TDA-2030/vesc-remote-controller/mininrf/O1CN01XpR0Wq1Qkuaa4X6eF_!!2658592015.png

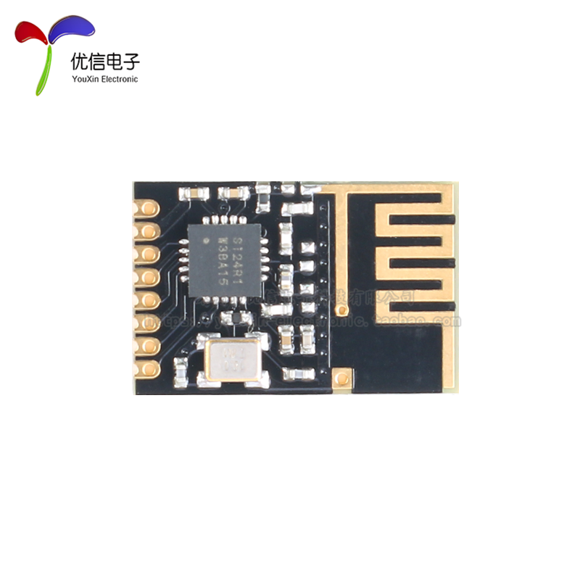
mininrf/O1CN01XpR0Wq1Qkuaa4X6eF_!!2658592015.png
