TDA-2030/vesc-remote-controller/mininrf/实物NRF.PNG

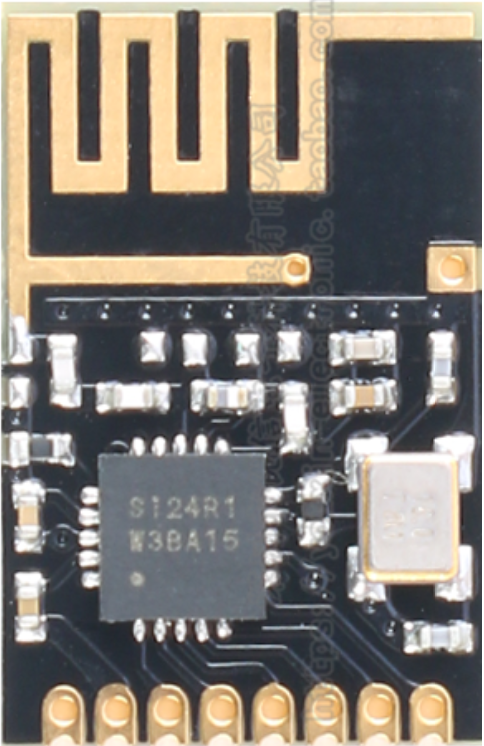
mininrf/实物NRF.PNG
