TDA-2030/vesc-remote-controller/mininrf/捕获.PNG

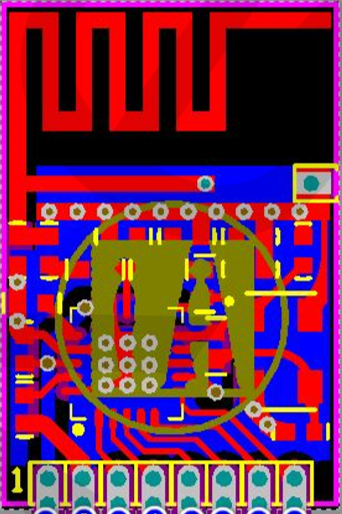
mininrf/捕获.PNG
