TDA-2030/vesc-remote-controller/PCB/TX-board-v2.0/STM8__TX.pdf

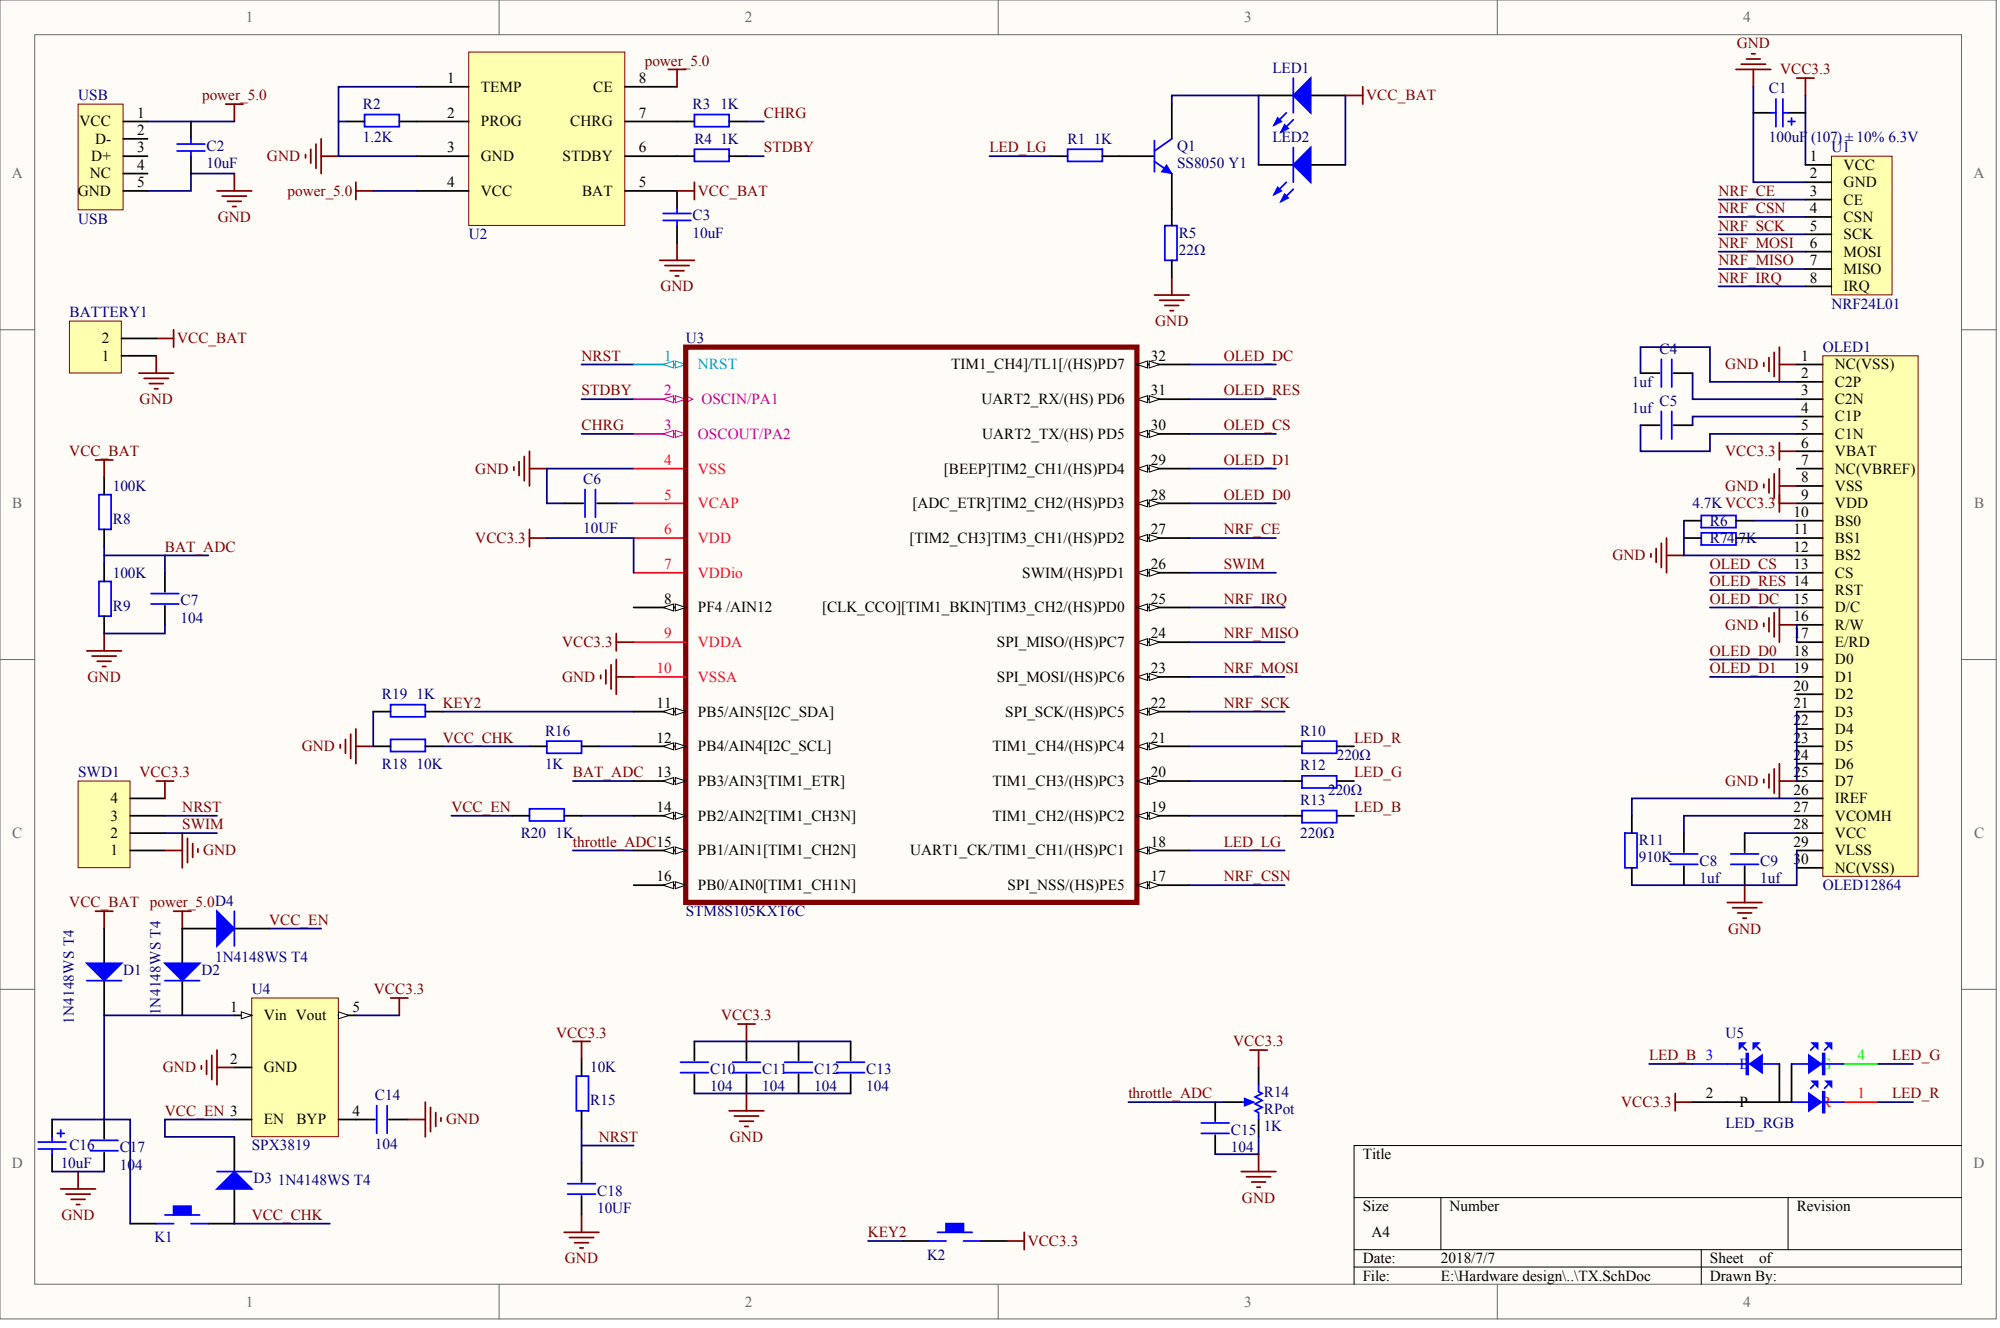
[picture p23: page 1]

VCOMH 27

VLSS 29

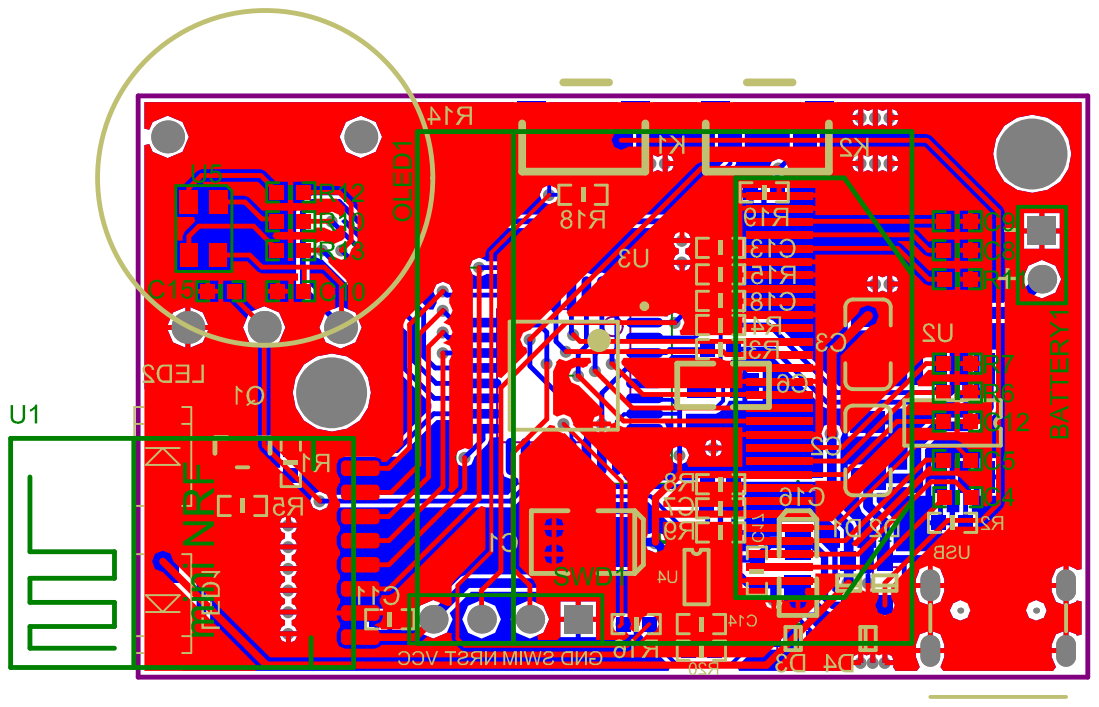
[picture p24: page 2]
