TDA-2030/vesc-remote-controller/PCB/RX-board-v1.0/STM8 remote.pdf

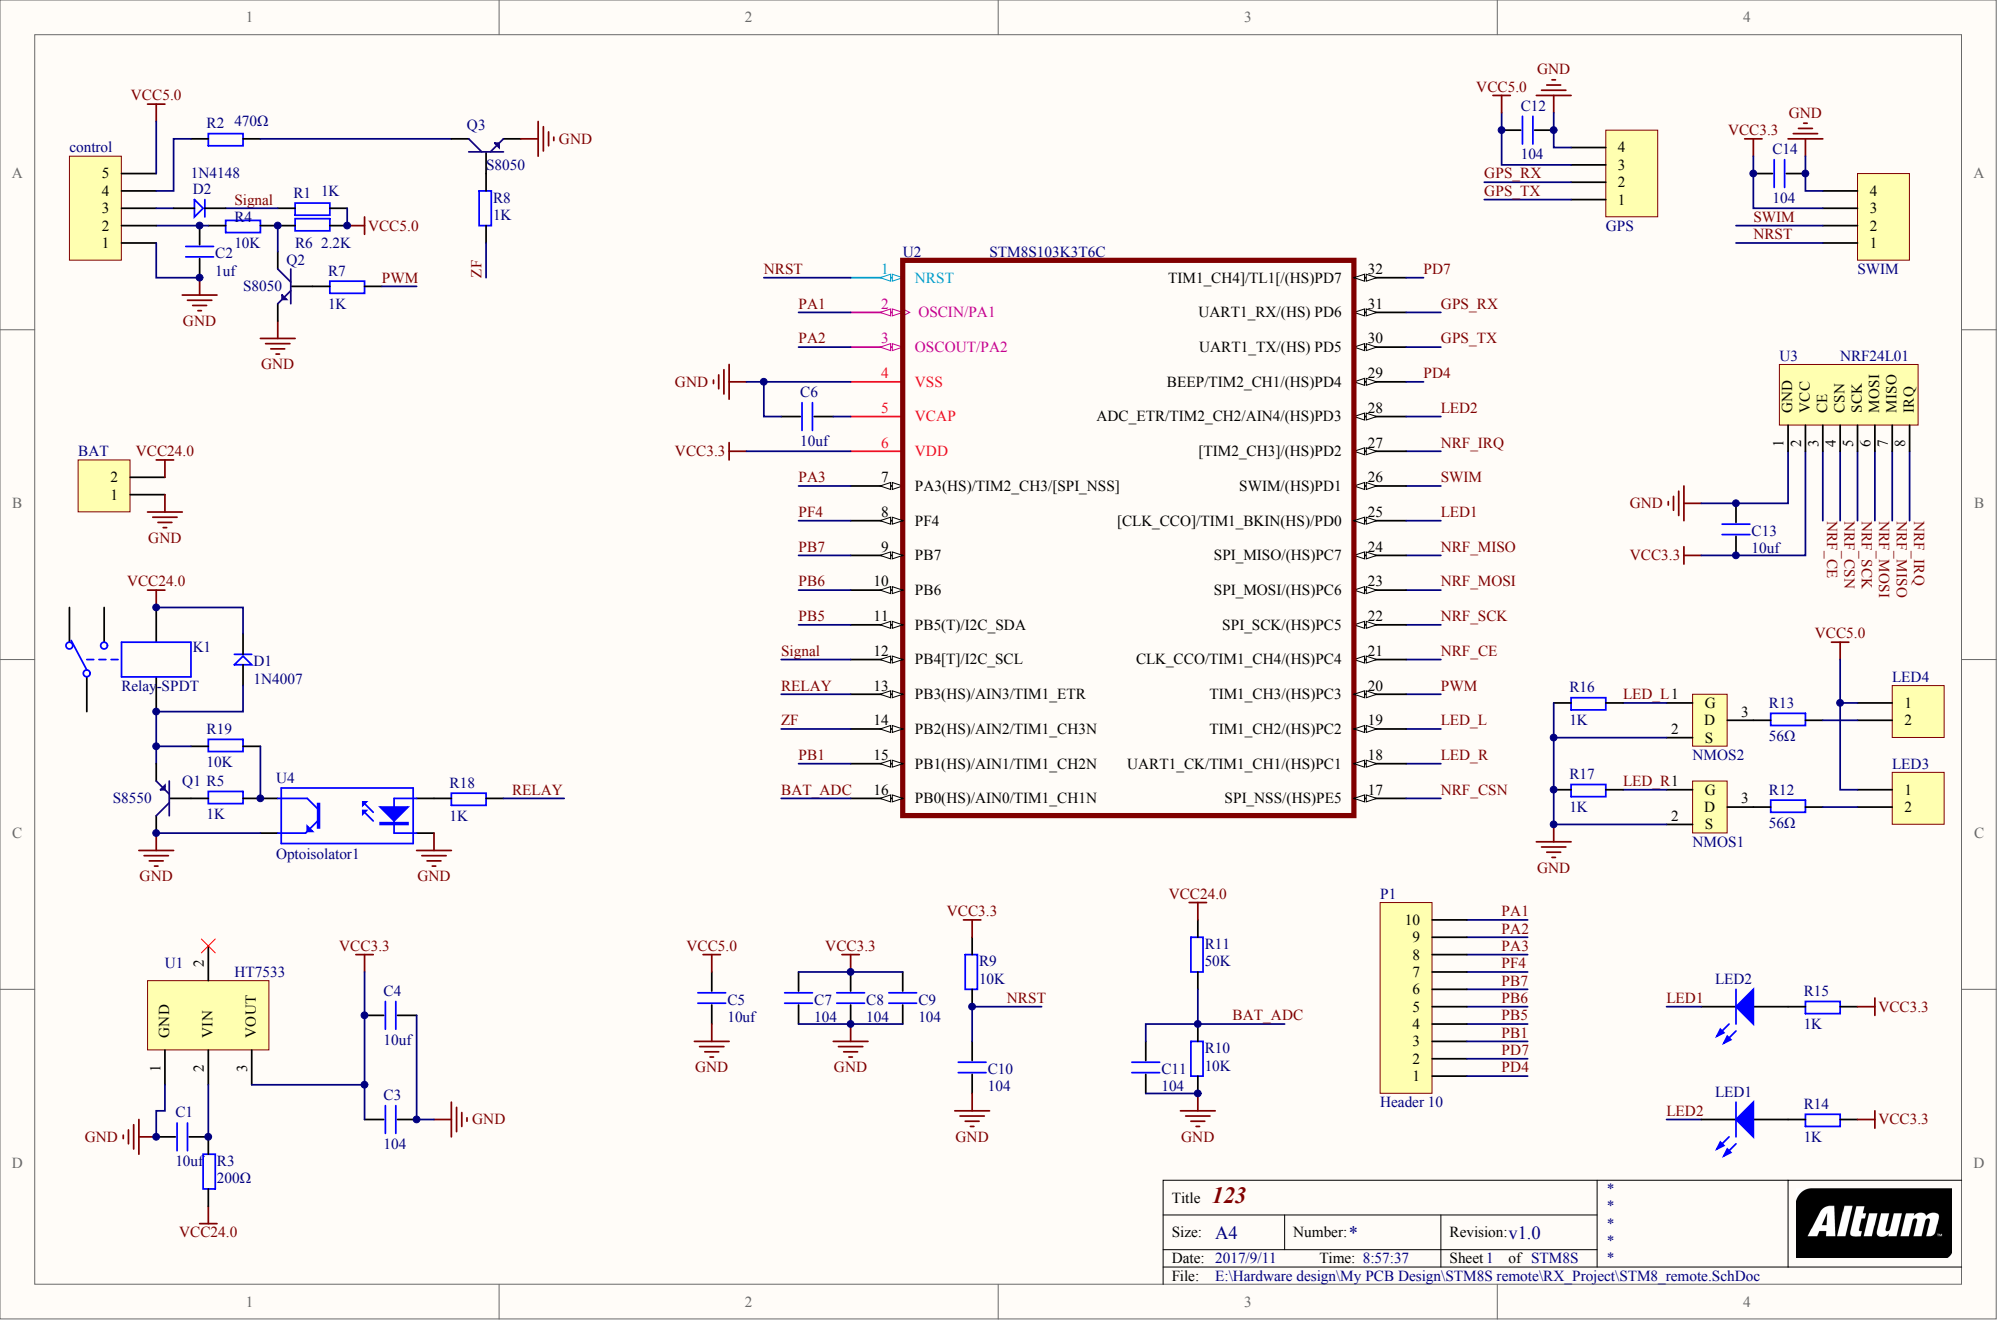
[picture p25: page 1]

123 Title | **** *

Size: A 4 | Number: * | Revision: v1.0

Date: File: 2017/9/11 Time: 8:57:37 | | Sheet 1 of STM8S

E:\Hardware design\My PCB Design\STM8S remote\RX_Project\STM8_remote.SchDoc

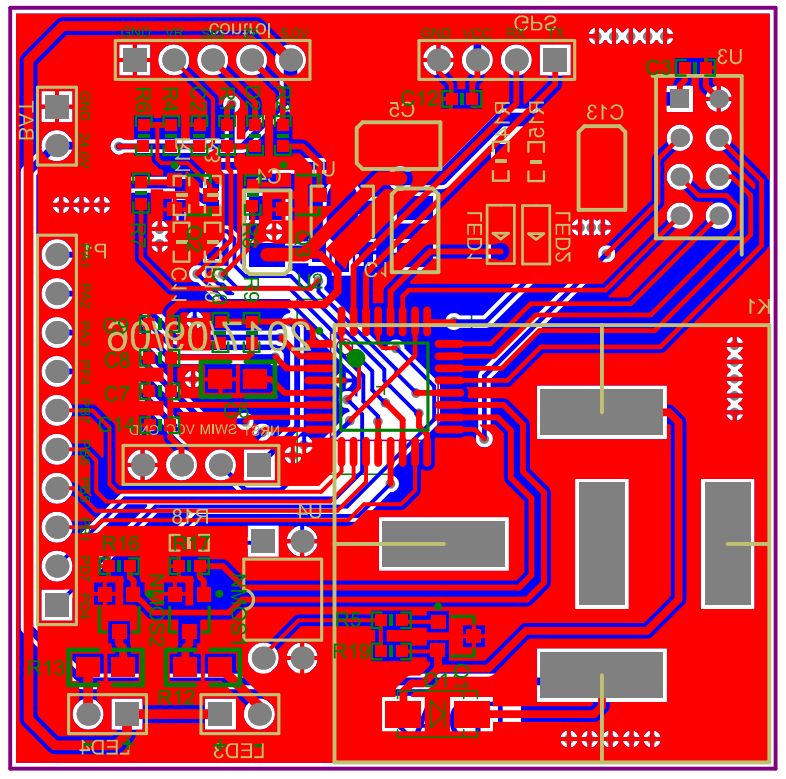
[picture p26: page 2]
