TDA-2030/vesc-remote-controller/PCB/RX-board-v2.0/RX.pdf

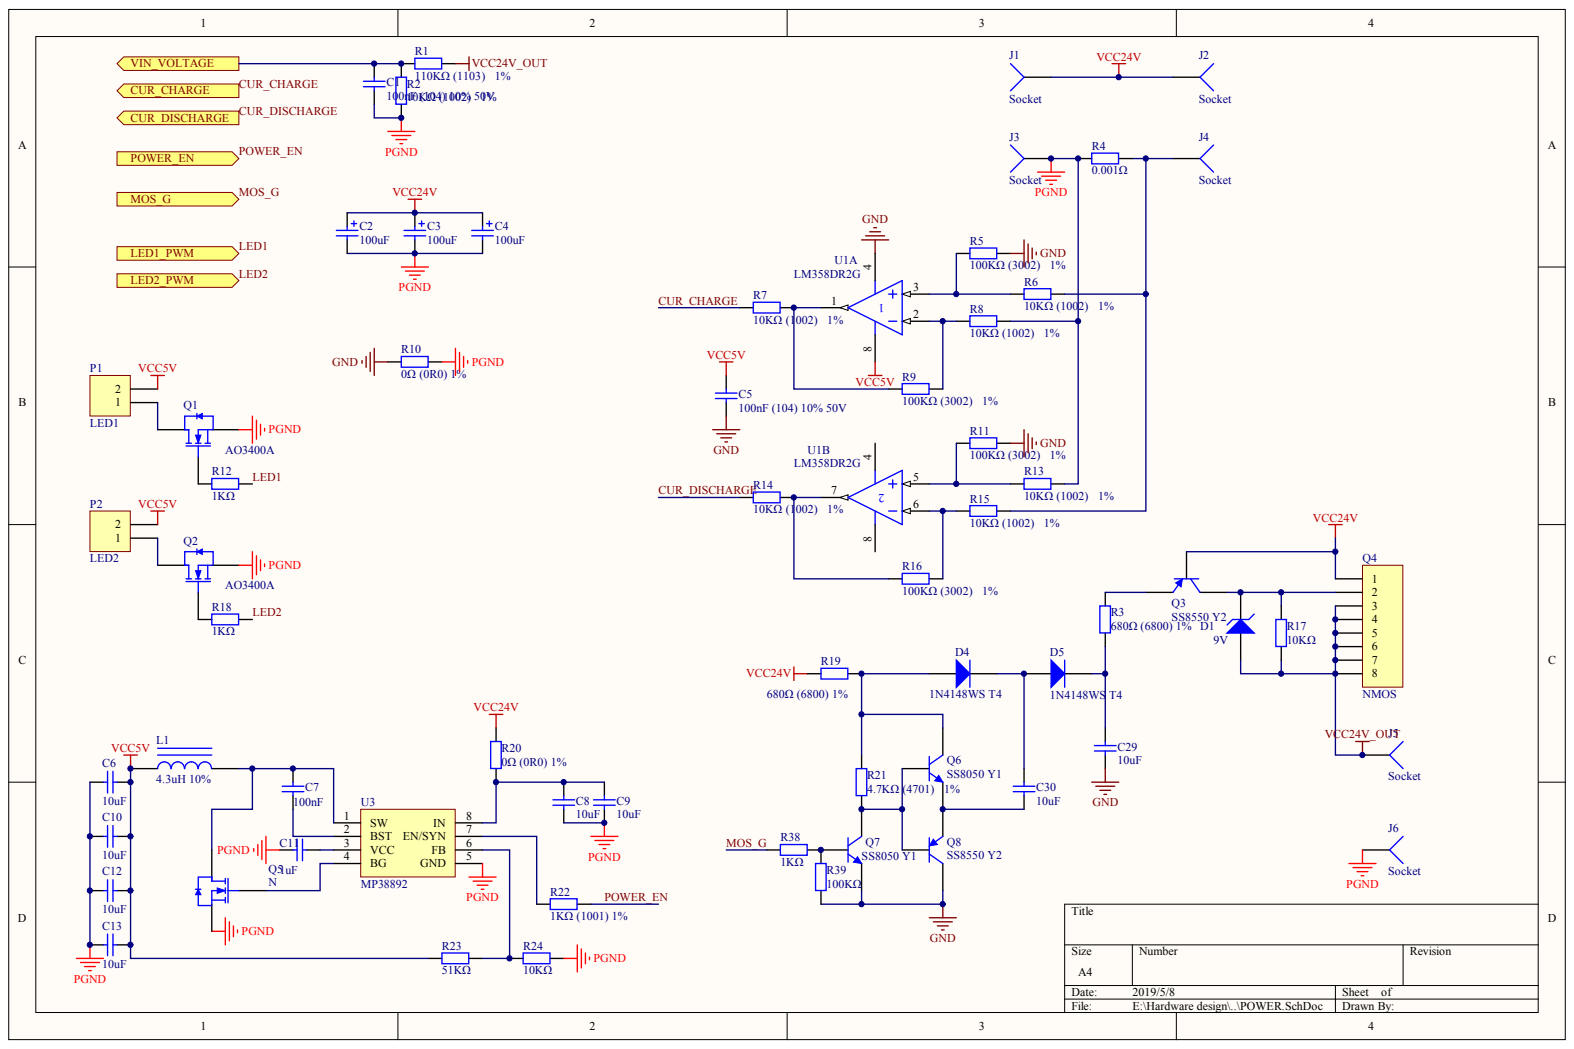
[picture p27: page 1]

Date: 2019/5/8 | Sheet of
File: E:\Hardware design\..\POWER.SchDoc | Drawn By:

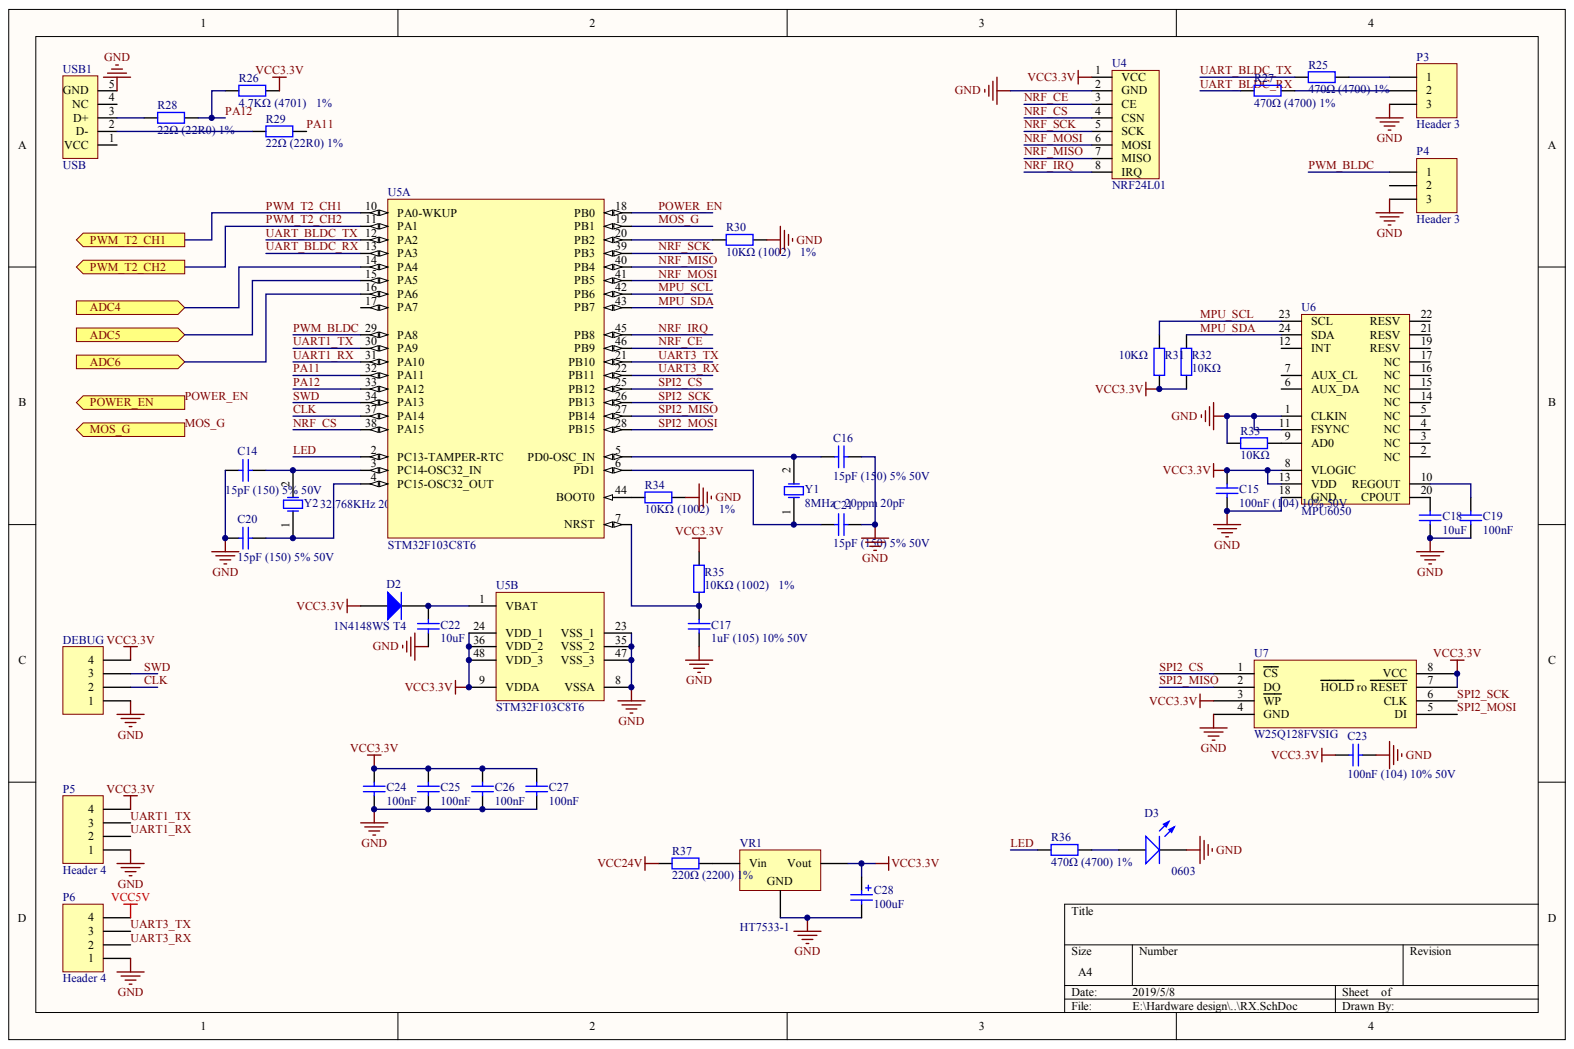
[picture p28: page 2]

PWM_BLDC | PA8 29

MPU_SDA | SDA 24

Size A4 | Number | Revision

Date: 2019/5/8 | Sheet of
File: E:\Hardware design\..\RX.SchDoc | Drawn By:

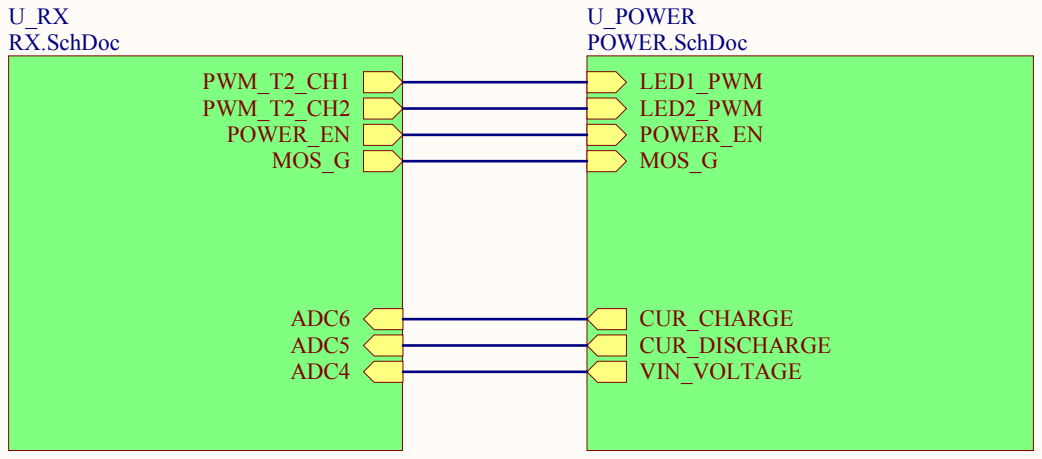
[picture p29: page 3]

Size A4 | Number | Revision

Date: 2019/5/8 | Sheet of
File: E:\Hardware design\..\TOP.SchDoc | Drawn By:

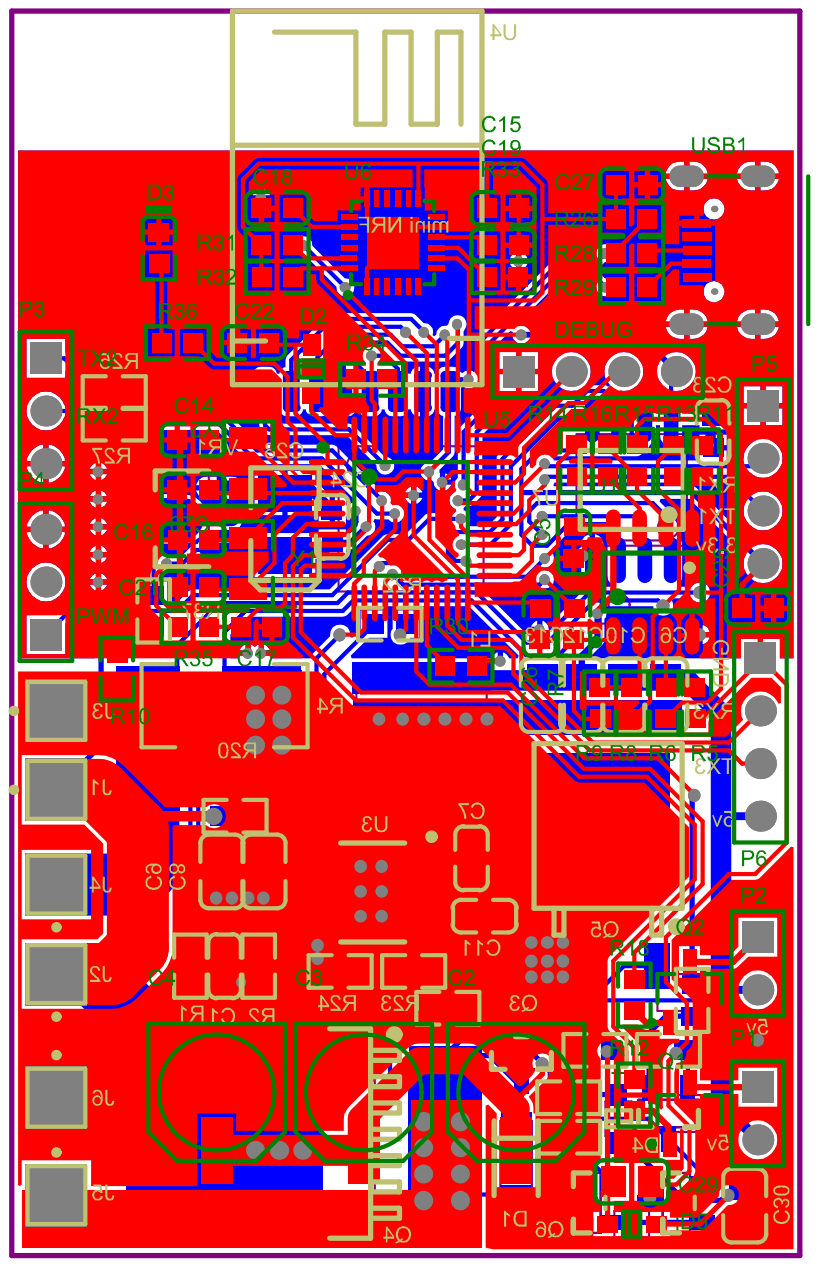
[picture p30: page 4]
