TDA-2030/vesc-remote-controller/PCB/RX-board-v4.0/RX.pdf

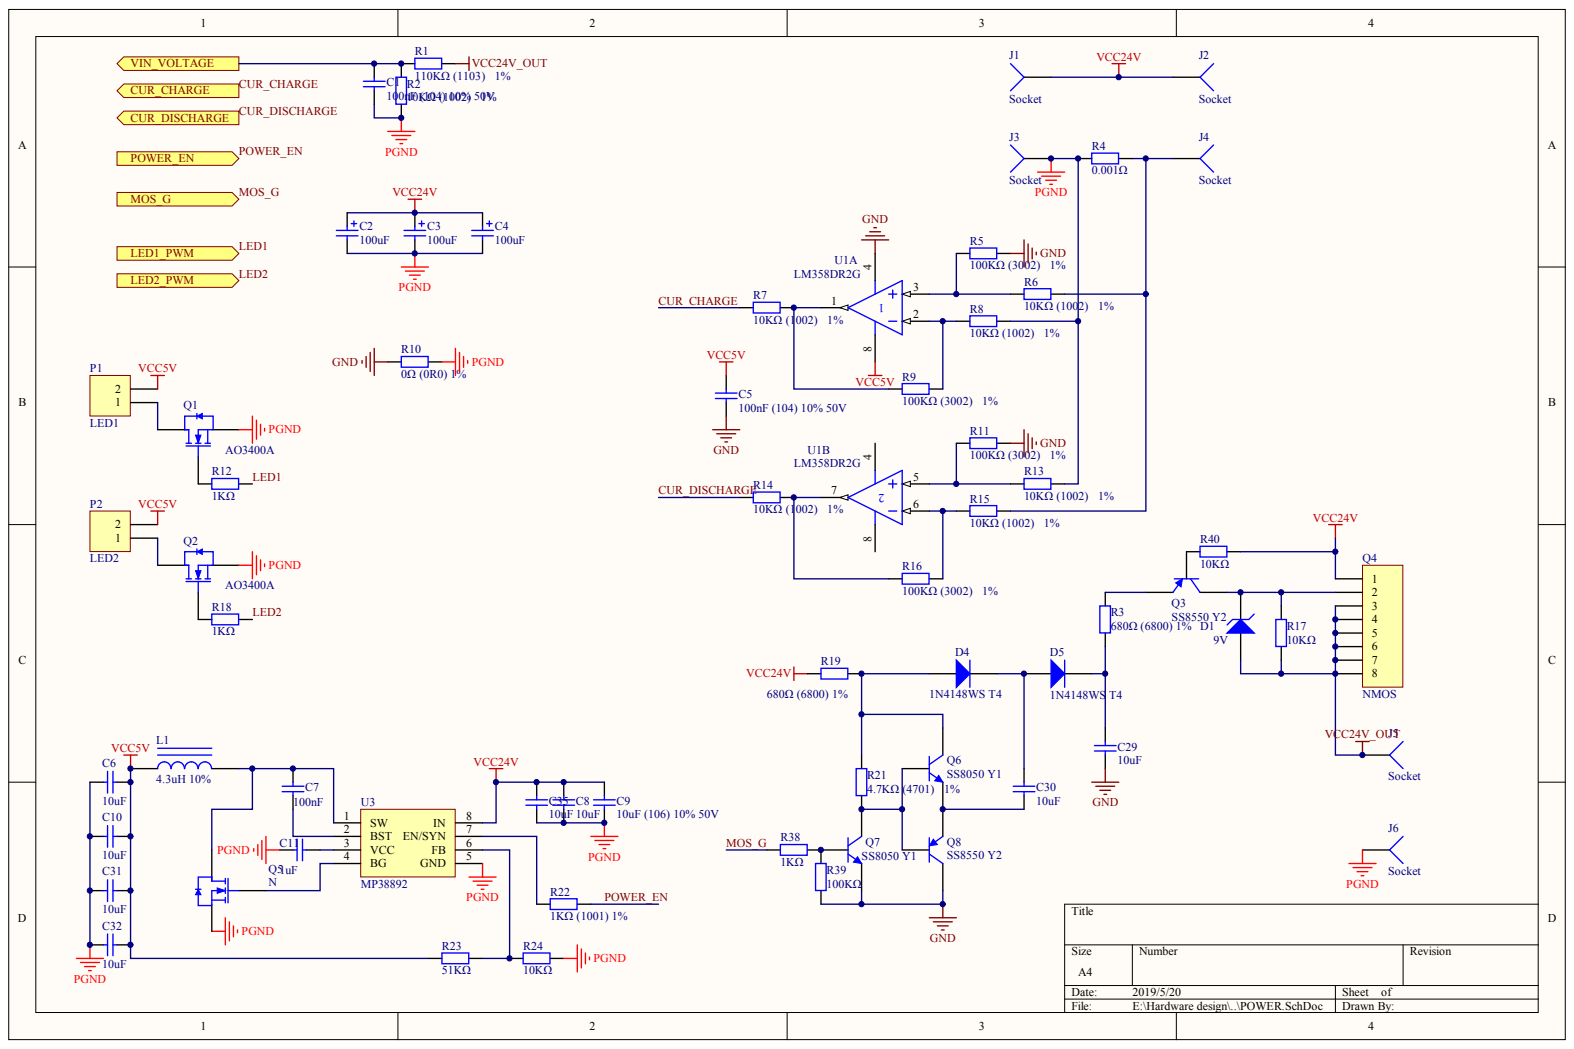
[picture p31: page 1]

Date: 2019/5/20 | Sheet of
File: E:\Hardware design\..\POWER.SchDoc | Drawn By:

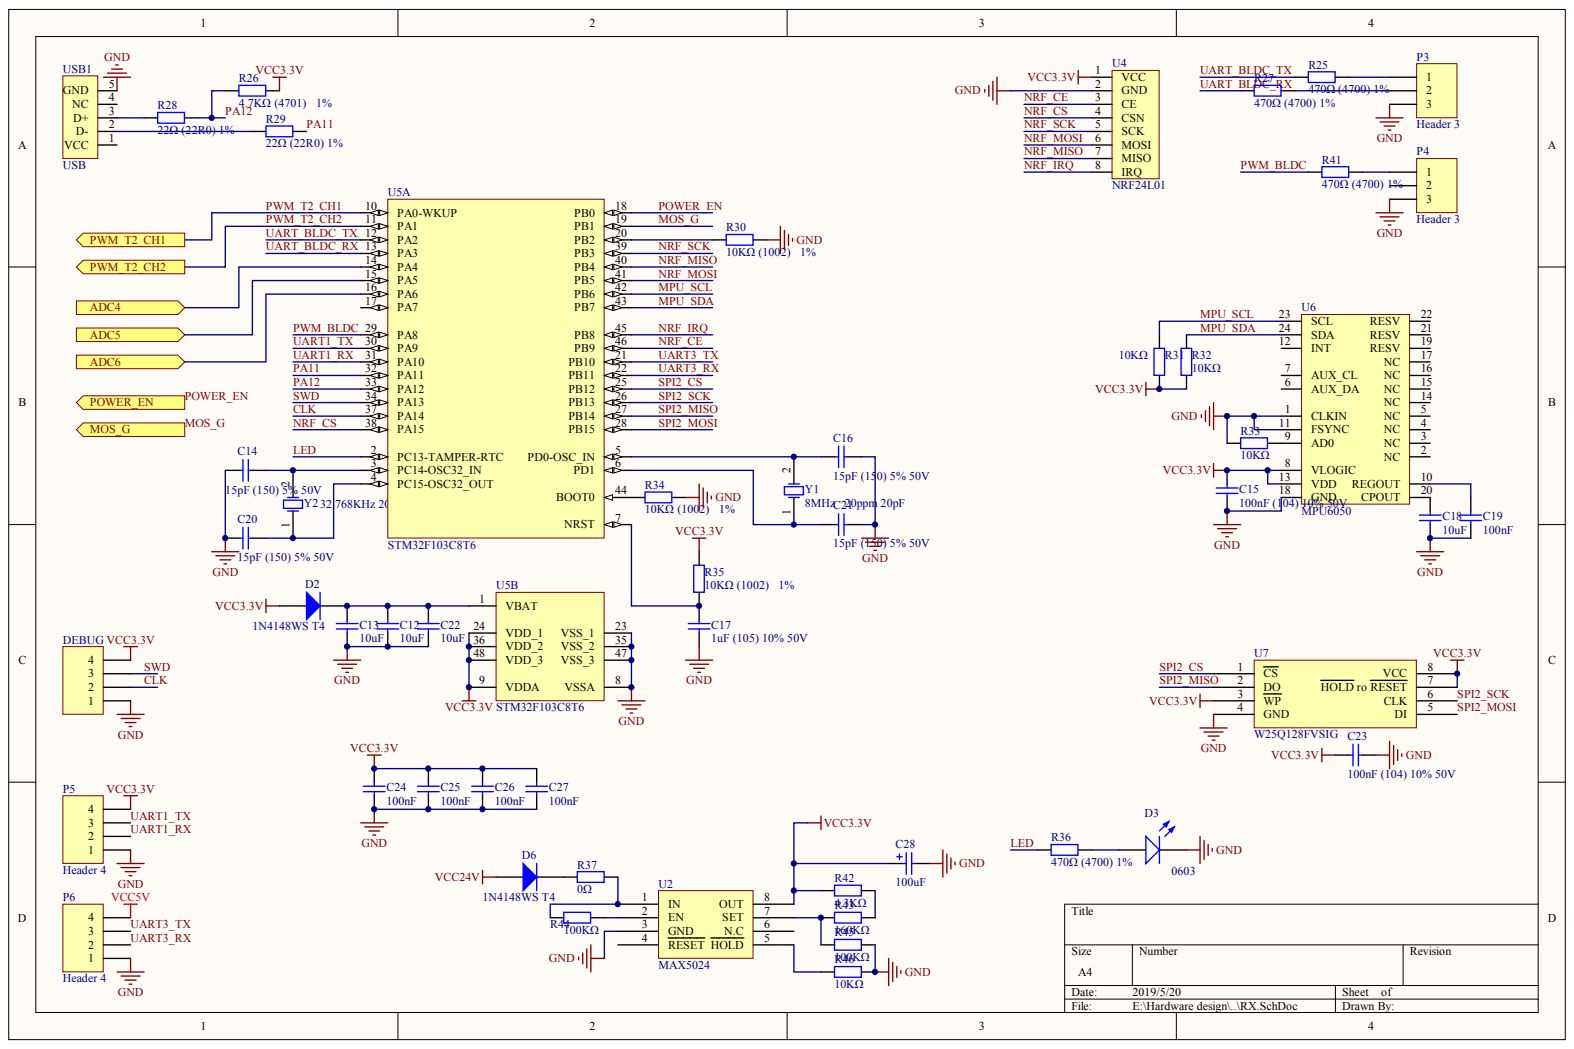
[picture p32: page 2]

PWM_BLDC | PA8 29

MPU_SDA | SDA 24

Size A4 | Number | Revision

Date: 2019/5/20 | Sheet of
File: E:\Hardware design\..\RX.SchDoc | Drawn By:


Size A4 | Number | Revision

Date: 2019/5/20 | Sheet of
File: E:\Hardware design\..\TOP.SchDoc | Drawn By:

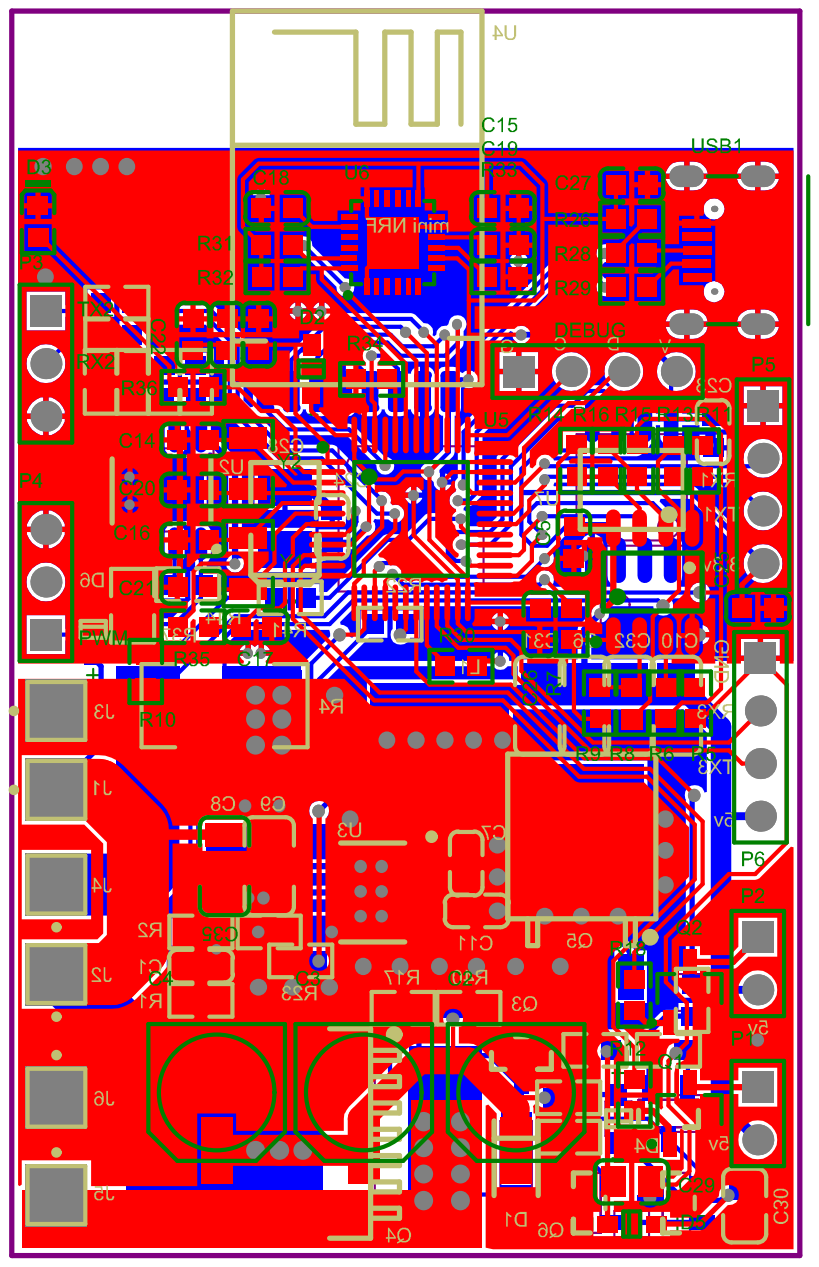
[picture p33: page 4]
