TDA-2030/vesc-remote-controller/receiver/code-L051K8U6/Src/tim.c

/**
  ******************************************************************************
  * File Name          : TIM.c
  * Description        : This file provides code for the configuration
  *                      of the TIM instances.
  ******************************************************************************
  * @attention
  *
  * <h2><center>&copy; Copyright (c) 2020 STMicroelectronics.
  * All rights reserved.</center></h2>
  *
  * This software component is licensed by ST under BSD 3-Clause license,
  * the "License"; You may not use this file except in compliance with the
  * License. You may obtain a copy of the License at:
  *                        opensource.org/licenses/BSD-3-Clause
  *
  ******************************************************************************
  */

/* Includes ------------------------------------------------------------------*/
#include "tim.h"

TIM_HandleTypeDef htim2;
TIM_HandleTypeDef htim6;
TIM_HandleTypeDef htim22;

/* TIM2 init function */
void MX_TIM2_Init(void)
{
  TIM_ClockConfigTypeDef sClockSourceConfig = {0};
  TIM_MasterConfigTypeDef sMasterConfig = {0};
  TIM_OC_InitTypeDef sConfigOC = {0};

  htim2.Instance = TIM2;
  htim2.Init.Prescaler = 31;
  htim2.Init.CounterMode = TIM_COUNTERMODE_UP;
  htim2.Init.Period = 19999;
  htim2.Init.ClockDivision = TIM_CLOCKDIVISION_DIV1;
  htim2.Init.AutoReloadPreload = TIM_AUTORELOAD_PRELOAD_ENABLE;
  if (HAL_TIM_Base_Init(&htim2) != HAL_OK)
  {
    Error_Handler();
  }
  sClockSourceConfig.ClockSource = TIM_CLOCKSOURCE_INTERNAL;
  if (HAL_TIM_ConfigClockSource(&htim2, &sClockSourceConfig) != HAL_OK)
  {
    Error_Handler();
  }
  if (HAL_TIM_PWM_Init(&htim2) != HAL_OK)
  {
    Error_Handler();
  }
  sMasterConfig.MasterOutputTrigger = TIM_TRGO_RESET;
  sMasterConfig.MasterSlaveMode = TIM_MASTERSLAVEMODE_DISABLE;
  if (HAL_TIMEx_MasterConfigSynchronization(&htim2, &sMasterConfig) != HAL_OK)
  {
    Error_Handler();
  }
  sConfigOC.OCMode = TIM_OCMODE_PWM1;
  sConfigOC.Pulse = 1500;
  sConfigOC.OCPolarity = TIM_OCPOLARITY_HIGH;
  sConfigOC.OCFastMode = TIM_OCFAST_DISABLE;
  if (HAL_TIM_PWM_ConfigChannel(&htim2, &sConfigOC, TIM_CHANNEL_1) != HAL_OK)
  {
    Error_Handler();
  }
  if (HAL_TIM_PWM_ConfigChannel(&htim2, &sConfigOC, TIM_CHANNEL_2) != HAL_OK)
  {
    Error_Handler();
  }
  if (HAL_TIM_PWM_ConfigChannel(&htim2, &sConfigOC, TIM_CHANNEL_4) != HAL_OK)
  {
    Error_Handler();
  }
  HAL_TIM_MspPostInit(&htim2);

}
/* TIM6 init function */
void MX_TIM6_Init(void)
{
  TIM_MasterConfigTypeDef sMasterConfig = {0};

  htim6.Instance = TIM6;
  htim6.Init.Prescaler = 31;
  htim6.Init.CounterMode = TIM_COUNTERMODE_UP;
  htim6.Init.Period = 4999;
  htim6.Init.AutoReloadPreload = TIM_AUTORELOAD_PRELOAD_ENABLE;
  if (HAL_TIM_Base_Init(&htim6) != HAL_OK)
  {
    Error_Handler();
  }
  sMasterConfig.MasterOutputTrigger = TIM_TRGO_RESET;
  sMasterConfig.MasterSlaveMode = TIM_MASTERSLAVEMODE_DISABLE;
  if (HAL_TIMEx_MasterConfigSynchronization(&htim6, &sMasterConfig) != HAL_OK)
  {
    Error_Handler();
  }

}
/* TIM22 init function */
void MX_TIM22_Init(void)
{
  TIM_ClockConfigTypeDef sClockSourceConfig = {0};
  TIM_MasterConfigTypeDef sMasterConfig = {0};
  TIM_OC_InitTypeDef sConfigOC = {0};

  htim22.Instance = TIM22;
  htim22.Init.Prescaler = 31;
  htim22.Init.CounterMode = TIM_COUNTERMODE_UP;
  htim22.Init.Period = 999;
  htim22.Init.ClockDivision = TIM_CLOCKDIVISION_DIV1;
  htim22.Init.AutoReloadPreload = TIM_AUTORELOAD_PRELOAD_ENABLE;
  if (HAL_TIM_Base_Init(&htim22) != HAL_OK)
  {
    Error_Handler();
  }
  sClockSourceConfig.ClockSource = TIM_CLOCKSOURCE_INTERNAL;
  if (HAL_TIM_ConfigClockSource(&htim22, &sClockSourceConfig) != HAL_OK)
  {
    Error_Handler();
  }
  if (HAL_TIM_OC_Init(&htim22) != HAL_OK)
  {
    Error_Handler();
  }
  sMasterConfig.MasterOutputTrigger = TIM_TRGO_RESET;
  sMasterConfig.MasterSlaveMode = TIM_MASTERSLAVEMODE_DISABLE;
  if (HAL_TIMEx_MasterConfigSynchronization(&htim22, &sMasterConfig) != HAL_OK)
  {
    Error_Handler();
  }
  sConfigOC.OCMode = TIM_OCMODE_TIMING;
  sConfigOC.Pulse = 500;
  sConfigOC.OCPolarity = TIM_OCPOLARITY_HIGH;
  sConfigOC.OCFastMode = TIM_OCFAST_DISABLE;
  if (HAL_TIM_OC_ConfigChannel(&htim22, &sConfigOC, TIM_CHANNEL_1) != HAL_OK)
  {
    Error_Handler();
  }
  HAL_TIM_MspPostInit(&htim22);

}

void HAL_TIM_Base_MspInit(TIM_HandleTypeDef* tim_baseHandle)
{

  if(tim_baseHandle->Instance==TIM2)
  {
    /* TIM2 clock enable */
    __HAL_RCC_TIM2_CLK_ENABLE();
  }
  else if(tim_baseHandle->Instance==TIM6)
  {
    /* TIM6 clock enable */
    __HAL_RCC_TIM6_CLK_ENABLE();

    /* TIM6 interrupt Init */
    HAL_NVIC_SetPriority(TIM6_DAC_IRQn, 0, 0);
    HAL_NVIC_EnableIRQ(TIM6_DAC_IRQn);
  }
  else if(tim_baseHandle->Instance==TIM22)
  {
    /* TIM22 clock enable */
    __HAL_RCC_TIM22_CLK_ENABLE();
  }
}
void HAL_TIM_MspPostInit(TIM_HandleTypeDef* timHandle)
{

  GPIO_InitTypeDef GPIO_InitStruct = {0};
  if(timHandle->Instance==TIM2)
  {
    __HAL_RCC_GPIOA_CLK_ENABLE();
    /**TIM2 GPIO Configuration    
    PA0     ------> TIM2_CH1
    PA1     ------> TIM2_CH2
    PA3     ------> TIM2_CH4 
    */
    GPIO_InitStruct.Pin = GPIO_PIN_0|GPIO_PIN_1|GPIO_PIN_3;
    GPIO_InitStruct.Mode = GPIO_MODE_AF_PP;
    GPIO_InitStruct.Pull = GPIO_NOPULL;
    GPIO_InitStruct.Speed = GPIO_SPEED_FREQ_LOW;
    GPIO_InitStruct.Alternate = GPIO_AF2_TIM2;
    HAL_GPIO_Init(GPIOA, &GPIO_InitStruct);

  }
  else if(timHandle->Instance==TIM22)
  {
  
    __HAL_RCC_GPIOB_CLK_ENABLE();
    /**TIM22 GPIO Configuration    
    PB4     ------> TIM22_CH1 
    */
    GPIO_InitStruct.Pin = GPIO_PIN_4;
    GPIO_InitStruct.Mode = GPIO_MODE_AF_PP;
    GPIO_InitStruct.Pull = GPIO_NOPULL;
    GPIO_InitStruct.Speed = GPIO_SPEED_FREQ_LOW;
    GPIO_InitStruct.Alternate = GPIO_AF4_TIM22;
    HAL_GPIO_Init(GPIOB, &GPIO_InitStruct);

  }

}

void HAL_TIM_Base_MspDeInit(TIM_HandleTypeDef* tim_baseHandle)
{

  if(tim_baseHandle->Instance==TIM2)
  {
    /* Peripheral clock disable */
    __HAL_RCC_TIM2_CLK_DISABLE();
  }
  else if(tim_baseHandle->Instance==TIM6)
  {
    /* Peripheral clock disable */
    __HAL_RCC_TIM6_CLK_DISABLE();

    /* TIM6 interrupt Deinit */
    HAL_NVIC_DisableIRQ(TIM6_DAC_IRQn);
  }
  else if(tim_baseHandle->Instance==TIM22)
  {
    /* Peripheral clock disable */
    __HAL_RCC_TIM22_CLK_DISABLE();
  }
} 

/* USER CODE BEGIN 1 */

void throttle_init(void)
{
	MX_TIM2_Init();
	HAL_TIM_PWM_Start(&htim2, TIM_CHANNEL_1);
	__HAL_TIM_SetCompare(&htim2, TIM_CHANNEL_1, 0);
}

void throttle_set(uint16_t throttle)
{
	
	if(throttle>THROTTLE_MAX)
	{
		throttle = THROTTLE_MAX;
	}
	__HAL_TIM_SetCompare(&htim2, TIM_CHANNEL_1, 999+throttle);
}



void bootstrap_init(void)
{
	MX_TIM22_Init();
	HAL_TIM_PWM_Start(&htim22, TIM_CHANNEL_1);
	__HAL_TIM_SetCompare(&htim22, TIM_CHANNEL_1, 0);
}

void bootstrap_enable(uint8_t state)
{
	GPIO_InitTypeDef GPIO_InitStruct = {0};
	if(state)
	{
		
		GPIO_InitStruct.Pin = GPIO_PIN_4;
		GPIO_InitStruct.Mode = GPIO_MODE_AF_PP;
		GPIO_InitStruct.Pull = GPIO_NOPULL;
		GPIO_InitStruct.Speed = GPIO_SPEED_FREQ_LOW;
		GPIO_InitStruct.Alternate = GPIO_AF4_TIM22;
		HAL_GPIO_Init(GPIOB, &GPIO_InitStruct);
		
		HAL_TIM_PWM_Start(&htim22, TIM_CHANNEL_1);
	}
	else
	{
		
		HAL_TIM_PWM_Stop(&htim22, TIM_CHANNEL_1);
		
		GPIO_InitStruct.Pin = GPIO_PIN_4;
		GPIO_InitStruct.Mode = GPIO_MODE_INPUT;
		GPIO_InitStruct.Pull = GPIO_PULLDOWN;		
		GPIO_InitStruct.Speed = GPIO_SPEED_FREQ_LOW;
		HAL_GPIO_Init(GPIOB, &GPIO_InitStruct);
	}
}

uint8_t bootstrap_isenable(void)
{
	return ((&htim22)->Instance->CR1 & TIM_CR1_CEN)?1:0;
}


void light_init(void)
{
	//MX_TIM2_Init();  //油门那里已经初始化了
	HAL_TIM_PWM_Start(&htim2, TIM_CHANNEL_2);
	HAL_TIM_PWM_Start(&htim2, TIM_CHANNEL_4);
	__HAL_TIM_SetCompare(&htim2, TIM_CHANNEL_2, 0);
	__HAL_TIM_SetCompare(&htim2, TIM_CHANNEL_4, 0);
}

void light_set(uint8_t ch ,uint32_t val)
{
	if(val>100)val=100;
	if(1 == ch)
	{
		__HAL_TIM_SetCompare(&htim2, TIM_CHANNEL_2, val*1000/100);
	}
	else if(2 == ch)
	{
		__HAL_TIM_SetCompare(&htim2, TIM_CHANNEL_4, val*1000/100);
	}
}
/* USER CODE END 1 */

/************************ (C) COPYRIGHT STMicroelectronics *****END OF FILE****/
