TDA-2030/vesc-remote-controller/transmitter/code-STM8S/Source/inc/main.h

/*
 * @Author: zhouli
 * @Date: 2020-04-04 15:28:44
 * @LastEditTime: 2020-06-03 00:06:13
 * @Description: file content
 */ 


#ifndef _MAIN_H__
#define _MAIN_H__

#define SETTING_FLASH_ADDR (0)
#define FLASH_CHECK (0x1278)   //检验值

#define MAJOR_VERSION 2
#define MINOR_VERSION 1


typedef struct
{
    uint16_t check;

    uint32_t *dashboard_p1;
    uint32_t *dashboard_p2;
    uint8_t light_en;
    uint8_t light1;
    uint8_t light2;

    uint16_t auto_off_time;

} Setting_TypeDef;
extern Setting_TypeDef setting;


typedef struct
{
    volatile uint8_t state;
    uint16_t auto_off_timer;
	uint16_t bat_vol;

} System_TypeDef;
extern System_TypeDef system;

typedef enum
{
    SYSTEM_STATE_IDLE,     //已连接，未开机
    SYSTEM_STATE_RUNNING,  //运行中
    SYSTEM_STATE_CHARGING, //充电中
    SYSTEM_STATE_NO_SIGNAL,//信号丢失
};

extern uint32_t Sys_Time;

void setting_write(void);
void setting_read(void);

#endif
