TDA-2030/vesc-remote-controller/receiver/code-L051K8U6/Src/rtc.c

/**
  ******************************************************************************
  * File Name          : RTC.c
  * Description        : This file provides code for the configuration
  *                      of the RTC instances.
  ******************************************************************************
  * @attention
  *
  * <h2><center>&copy; Copyright (c) 2020 STMicroelectronics.
  * All rights reserved.</center></h2>
  *
  * This software component is licensed by ST under BSD 3-Clause license,
  * the "License"; You may not use this file except in compliance with the
  * License. You may obtain a copy of the License at:
  *                        opensource.org/licenses/BSD-3-Clause
  *
  ******************************************************************************
  */

/* Includes ------------------------------------------------------------------*/
#include "rtc.h"

/* USER CODE BEGIN 0 */


_calendar_obj calendar;//ʱ�ӽṹ�� 


/* USER CODE END 0 */

RTC_HandleTypeDef hrtc;

/* RTC init function */
void MX_RTC_Init(void)
{
  RTC_TimeTypeDef sTime = {0};
  RTC_DateTypeDef sDate = {0};

  /** Initialize RTC Only 
  */
  hrtc.Instance = RTC;
  hrtc.Init.HourFormat = RTC_HOURFORMAT_24;
  hrtc.Init.AsynchPrediv = 127;
  hrtc.Init.SynchPrediv = 255;
  hrtc.Init.OutPut = RTC_OUTPUT_DISABLE;
  hrtc.Init.OutPutRemap = RTC_OUTPUT_REMAP_NONE;
  hrtc.Init.OutPutPolarity = RTC_OUTPUT_POLARITY_HIGH;
  hrtc.Init.OutPutType = RTC_OUTPUT_TYPE_OPENDRAIN;
  if (HAL_RTC_Init(&hrtc) != HAL_OK)
  {
    Error_Handler();
  }

  /** Initialize RTC and set the Time and Date 
  */
  sTime.Hours = 0;
  sTime.Minutes = 0;
  sTime.Seconds = 0;
  sTime.DayLightSaving = RTC_DAYLIGHTSAVING_NONE;
  sTime.StoreOperation = RTC_STOREOPERATION_RESET;
  if (HAL_RTC_SetTime(&hrtc, &sTime, RTC_FORMAT_BIN) != HAL_OK)
  {
    Error_Handler();
  }
  sDate.WeekDay = RTC_WEEKDAY_SUNDAY;
  sDate.Month = RTC_MONTH_MARCH;
  sDate.Date = 1;
  sDate.Year = 20;

  if (HAL_RTC_SetDate(&hrtc, &sDate, RTC_FORMAT_BIN) != HAL_OK)
  {
    Error_Handler();
  }
  /** Enable the WakeUp 
  */

}

void HAL_RTC_MspInit(RTC_HandleTypeDef* rtcHandle)
{

  if(rtcHandle->Instance==RTC)
  {
    /* RTC clock enable */
    __HAL_RCC_RTC_ENABLE();

    /* RTC interrupt Init */
    HAL_NVIC_SetPriority(RTC_IRQn, 0, 0);
    HAL_NVIC_EnableIRQ(RTC_IRQn);
  }
}

void HAL_RTC_MspDeInit(RTC_HandleTypeDef* rtcHandle)
{

  if(rtcHandle->Instance==RTC)
  {
    /* Peripheral clock disable */
    __HAL_RCC_RTC_DISABLE();

    /* RTC interrupt Deinit */
    HAL_NVIC_DisableIRQ(RTC_IRQn);
  }
} 

/* USER CODE BEGIN 1 */

void RTC_Get(void)
{
	RTC_DateTypeDef rtc_data;
	RTC_TimeTypeDef rtc_time;
	
	HAL_RTC_GetTime(&hrtc, &rtc_time, RTC_FORMAT_BIN);
	HAL_RTC_GetDate(&hrtc, &rtc_data, RTC_FORMAT_BIN);
	
	
	calendar.w_year = rtc_data.Year;
	calendar.w_month = rtc_data.Month;
	calendar.w_date = rtc_data.Date;
	
	calendar.hour = rtc_time.Hours;
	calendar.min = rtc_time.Minutes;
	calendar.sec = rtc_time.Seconds;
}

uint8_t RTC_Set(uint16_t syear,uint8_t smon,uint8_t sday,uint8_t hour,uint8_t min,uint8_t sec)
{
	RTC_DateTypeDef rtc_data;
	RTC_TimeTypeDef rtc_time;
	
	rtc_time.DayLightSaving = RTC_DAYLIGHTSAVING_NONE;
	rtc_time.StoreOperation = RTC_STOREOPERATION_RESET;
	
	rtc_data.Year = syear;
	rtc_data.Month = smon;
	rtc_data.Date = sday;
	
	rtc_time.Hours = hour;
	rtc_time.Minutes = min;
	rtc_time.Seconds = sec;
	
	HAL_RTC_SetTime(&hrtc, &rtc_time, RTC_FORMAT_BIN);
	HAL_RTC_SetDate(&hrtc, &rtc_data, RTC_FORMAT_BIN);
	return 0;
}

/* USER CODE END 1 */

/************************ (C) COPYRIGHT STMicroelectronics *****END OF FILE****/
