TDA-2030/vesc-remote-controller/mininrf/2.NRF24L01程序/NRF24L01程序/双按键测试程序/inc/delay.h

/****************************************Copyright (c)**************************************************
**                               Guangzhou ZHIYUAN electronics Co.,LTD.
**                                     
**                                 http://www.embedtools.com
**
**--------------File Info-------------------------------------------------------------------------------
** File Name:         
** Last modified Date: 
** Last Version:       v1.00
** Description:        
** 
**------------------------------------------------------------------------------------------------------
** Created By:         
** Created date:       
** Version:            v1.00
** Descriptions:
**
**------------------------------------------------------------------------------------------------------
** Modified by:        
** Modified date:       
** Version:             
** Description:        
**
********************************************************************************************************/
#ifndef __DELAY_H
#define __DELAY_H
#include "typedef.h"

void _delay_us(unsigned int _us);
void Delay100ms(void);

#endif
