TDA-2030/vesc-remote-controller/mininrf/2.NRF24L01程序/NRF24L01程序/双按键测试程序/source/delay.c

/******************************************************************************/
/*                        -- 深圳安信可科技有限公司 --                        */
/*
//  文件名：                                                              
//  说明：                                                                  
//  编写人员：                                                                   
//  编写日期：                                                              
//  程序维护：
//  维护记录：
//
//                                                          
*/ 
// 免责声明：该程序仅用于学习与交流 
// (c) Anxinke Corporation. All rights reserved.                                                               
/******************************************************************************/
#include "delay.h"



/******************************************************************************/
// 函数名称： 
// 输入参数： 
// 输出参数： 
// 函数功能： 
/******************************************************************************/
void Delay100ms(void)       //@22.1184MHz
{
	unsigned char i, j, k;
	_nop_();
	_nop_();
	i = 9;
	j = 104;
	k = 139;
	do
	{
		do
		{
			while (--k);
		} while (--j);
	} while (--i);
}

/******************************************************************************/
// 函数名称： 
// 输入参数： 
// 输出参数： 
// 函数功能： 
/******************************************************************************/
void _delay_us(unsigned int _us)
{
    char a=0;
    for(_us;_us;_us--)
        for(a=0;a<1;a++);
}
