TDA-2030/vesc-remote-controller/transmitter/code-STM8S/Source/inc/m_settings.h

/*
 * @Author: zhouli
 * @Date: 2020-04-18 16:14:46
 * @LastEditTime: 2020-04-18 16:17:23
 * @Description: file content
 */

#ifndef __M_SETTINGS_H
#define __M_SETTINGS_H


void page_setting(void);

#endif
