TDA-2030/vesc-remote-controller/transmitter/code-STM8S/Source/inc/stm8s_flash.h

  
  
#ifndef __STM8S_FLASH_H__
#define __STM8S_FLASH_H__


void EEPROM_write(uint8_t addr,const uint8_t *indata,uint8_t inlength);
void EEPROM_read(uint8_t addr,uint8_t *indata,uint8_t inlength);


#endif
