TDA-2030/vesc-remote-controller/receiver/code-L051K8U6/Src/stmflash.c

#include "main.h"
#include "stmflash.h"

 


//读取指定地址的字(32位数据) 
//faddr:读地址 
//返回值:对应数据.
static uint32_t STMFLASH_ReadWord(uint32_t faddr)
{
	return *(__IO uint32_t *)faddr; 
}


//从指定地址开始写入指定长度的数据
//OTP区域地址范围:0X1FF0F000~0X1FF0F41F
//WriteAddr:起始地址(此地址必须为4的倍数!!)
//pBuffer:数据指针
//NumToWrite:字(32位)数(就是要写入的32位数据的个数.) 
void STMFLASH_Write(uint32_t WriteAddr,uint32_t *pBuffer,uint32_t NumToWrite)	
{ 
    FLASH_EraseInitTypeDef FlashEraseInit;
    HAL_StatusTypeDef FlashStatus=HAL_OK;
    uint32_t SectorError=0;
	uint32_t addrx=0;
	uint32_t endaddr=0;	
    if(WriteAddr<FLASH_BASE||WriteAddr%4)return;	//非法地址
    
 	HAL_FLASH_Unlock();             //解锁	
	addrx=WriteAddr;				//写入的起始地址
	endaddr=WriteAddr+NumToWrite*4;	//写入的结束地址
    
    if(addrx<0X1FF00000)
    {
        while(addrx<endaddr)		//扫清一切障碍.(对非FFFFFFFF的地方,先擦除)
		{
			if(STMFLASH_ReadWord(addrx)!=0X00000000)//有非0XFFFFFFFF的地方,要擦除这个扇区
			{
                FlashEraseInit.TypeErase=FLASH_TYPEERASE_PAGES;       //擦除类型，扇区擦除 
                FlashEraseInit.NbPages=1;                             //一次只擦除一个扇区
				FlashStatus = HAL_FLASHEx_Erase(&FlashEraseInit,&SectorError);
                if(FlashStatus!=HAL_OK) 
                {
                    break ;//发生错误了	
                }
			}else
			{
				addrx+=4;
			}
        }
    }
	if(FlashStatus==HAL_OK)
	{
		while(WriteAddr<endaddr)//写数据
		{
            if(HAL_FLASH_Program(FLASH_TYPEPROGRAM_WORD,WriteAddr,*pBuffer)!=HAL_OK)//写入数据
			{ 
				break;	//写入异常
			}
			WriteAddr+=4;
			pBuffer++;
		} 
	}
	HAL_FLASH_Lock();           //上锁
} 

//从指定地址开始读出指定长度的数据
//ReadAddr:起始地址
//pBuffer:数据指针
//NumToRead:字(32位)数
void STMFLASH_Read(uint32_t ReadAddr,uint32_t *pBuffer,uint32_t NumToRead)   	
{
	uint32_t i;
	for(i=0;i<NumToRead;i++)
	{
		pBuffer[i]=STMFLASH_ReadWord(ReadAddr);//读取4个字节.
		ReadAddr+=4;//偏移4个字节.	
	}
}
