TDA-2030/vesc-remote-controller/receiver/code-L051K8U6/Inc/24l01_protocol.h

/*****************************************************************
*  @file     : xx.x            
*  @brief    :     
*  Details.          
*                       
*  @author   : zhouli        
*  @version  : xx.xx         
*  @date     : 2017-xx-xx    
*                           
*  Change History 
******************************************************************/
  
  
#ifndef __RF24L01_PROTOCOL_H__
#define __RF24L01_PROTOCOL_H__




void NRF24L01_Protocol_Exec(void);
void NRF24L01_Protocol_Irq_Handle(void);



#endif
