TDA-2030/vesc-remote-controller/transmitter/code-STM8S/Source/inc/gui.h

/*
 * @Author: zhouli
 * @Date: 2020-05-25 01:15:10
 * @LastEditTime: 2020-05-27 01:16:42
 * @Description: file content
 */ 
#ifndef  GUI_H_
#define  GUI_H_

#include "gui_basic.h"
#include "gui_bitmap.h"
#include "gui_char.h"
#include "gui_windows.h"
#include "gui_dashboard.h"

#endif
