TDA-2030/vesc-remote-controller/transmitter/code-STM8S/Source/inc/gui_dashboard.h

/*
 * @Author: zhouli
 * @Date: 2020-05-25 01:15:10
 * @LastEditTime: 2020-05-27 02:53:53
 * @Description: file content
 */ 
#ifndef  GUI_DASHBOARD_H
#define  GUI_DASHBOARD_H

void GUI_DashboardDraw(uint8_t db_index, uint16_t x0, uint16_t y0, uint8_t scale_num, uint16_t r);
void GUI_DashboardSetAngle(uint8_t db_index, uint8_t angle);

#endif
