TDA-2030/vesc-remote-controller/transmitter/code-STM8S/Source/inc/gui_windows.h

/*
 * @Author: zhouli
 * @Date: 2020-04-04 15:28:44
 * @LastEditTime: 2020-05-27 00:10:54
 * @Description: file content
 */ 
#ifndef __GUI_WINDOWS_H__
#define __GUI_WINDOWS_H__

typedef void (*win_fun_t)(void);
typedef enum
{
	WIN_STATE_INIT,
	WIN_STATE_EXEC,
	WIN_STATE_EXIT,
} win_state_e;

void win_init(void);
void win_exec(void);
void win_set(win_fun_t set);
win_fun_t win_get_current(void);
win_fun_t win_get_previous(void);
win_state_e win_get_state(void);
void win_set_flash_time(uint8_t n_ms);
void win_set_exec_callback(void (*cb)(void*));


#endif
