TDA-2030/vesc-remote-controller/transmitter/code-STM8S/Source/inc/gui_bitmap.h

/*
 * @Author: zhouli
 * @Date: 2020-05-25 01:15:10
 * @LastEditTime: 2020-05-26 00:09:48
 * @Description: file content
 */ 
#ifndef  GUI_BITMAP_H
#define  GUI_BITMAP_H

void GUI_DrawBMP(uint8_t x0, uint8_t y0, uint8_t width, uint8_t height, const uint8_t BMP[]);

#endif
